ABillBlakely/Wavetable-desktop-speaker-stand/photos/03_no_backstop.jpg

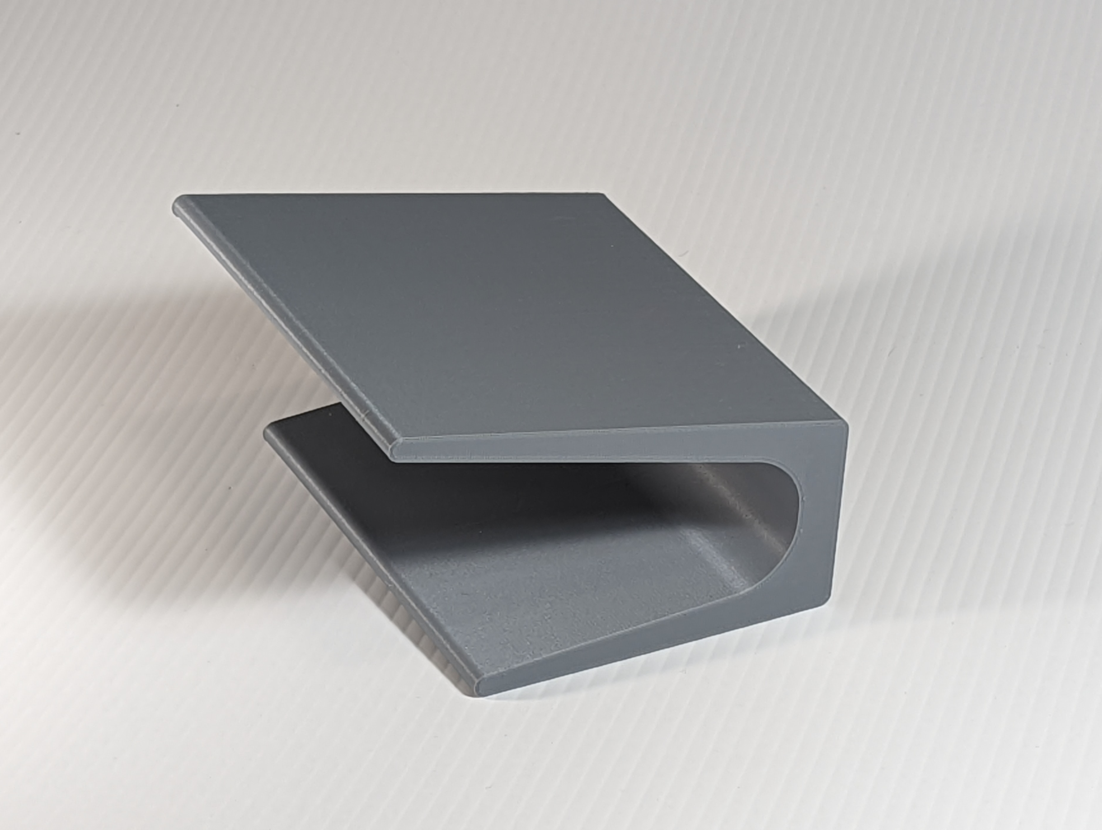
photos/03_no_backstop.jpg
