ABillBlakely/Wavetable-desktop-speaker-stand/photos/11_large_with_yamaha_hs80_detail.jpg

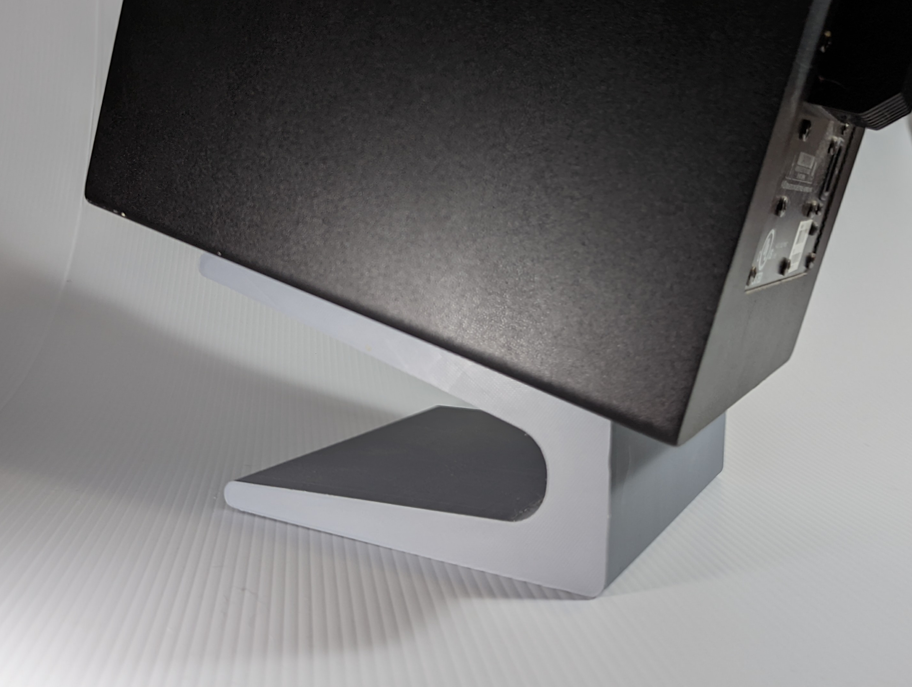
photos/11_large_with_yamaha_hs80_detail.jpg
